kevinlutzer/room-environment-monitor/documentation/v2/3d.png

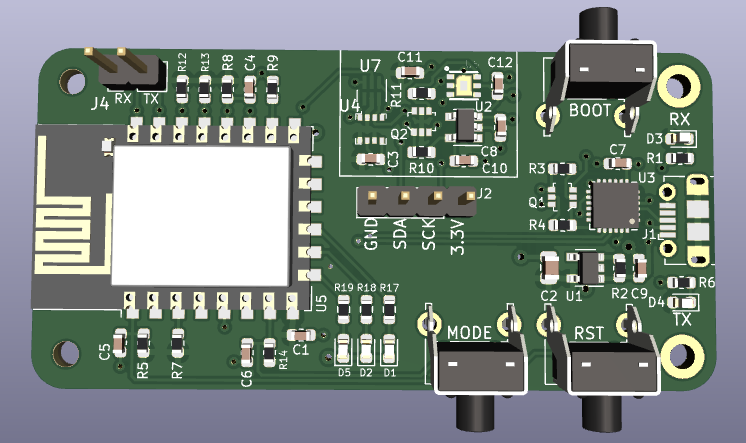
documentation/v2/3d.png
