kevinlutzer/room-environment-monitor/fab/v4/room-environment-monitor-v4/room_environment_monitor-F_Paste.pdf

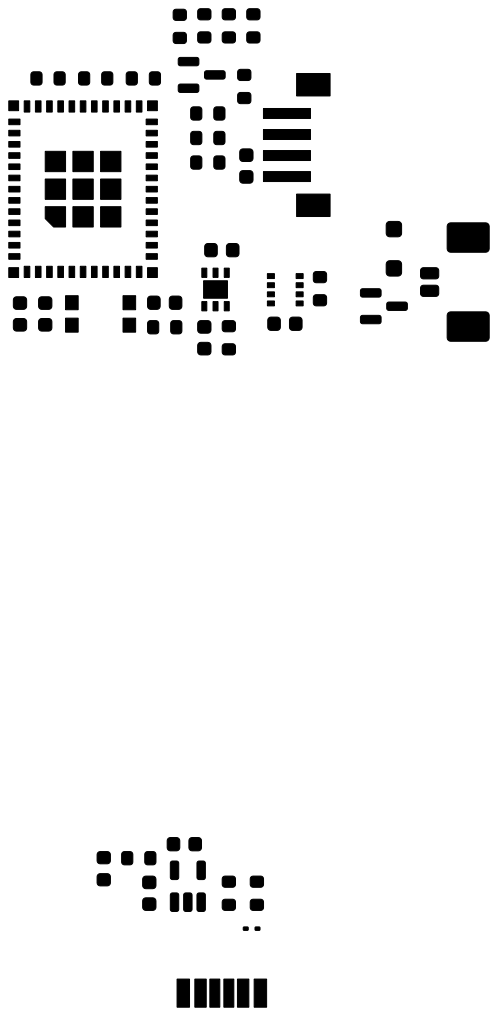
[picture p23: page 1]
