kevinlutzer/room-environment-monitor/fab/v4/room-environment-monitor-v4/room_environment_monitor-F_Silkscreen.pdf

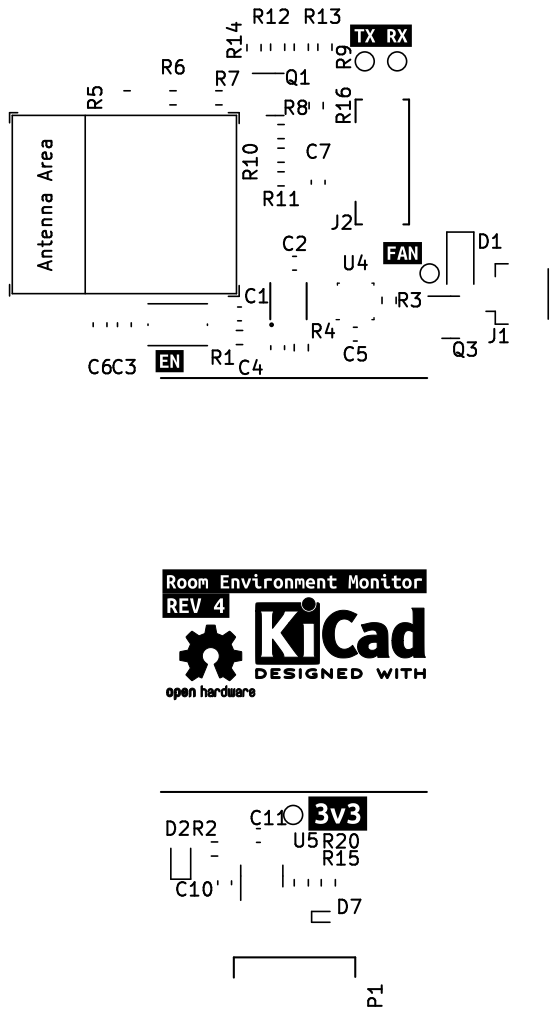
[picture p24: page 1]
