kevinlutzer/room-environment-monitor/fab/v4/room-environment-monitor-v4/room_environment_monitor-In1_Cu.pdf

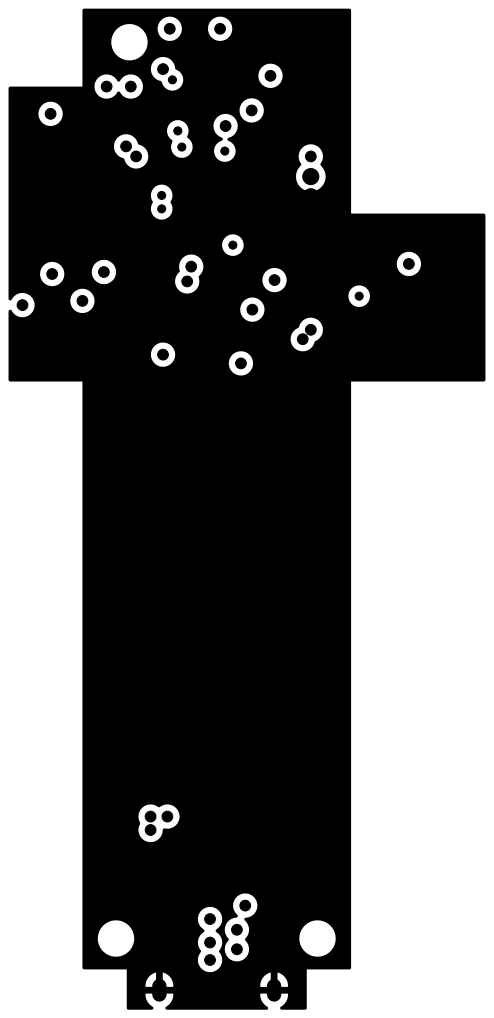
[picture p25: page 1]
