kevinlutzer/room-environment-monitor/fab/v4/room-environment-monitor-v4/room_environment_monitor-In2_Cu.pdf

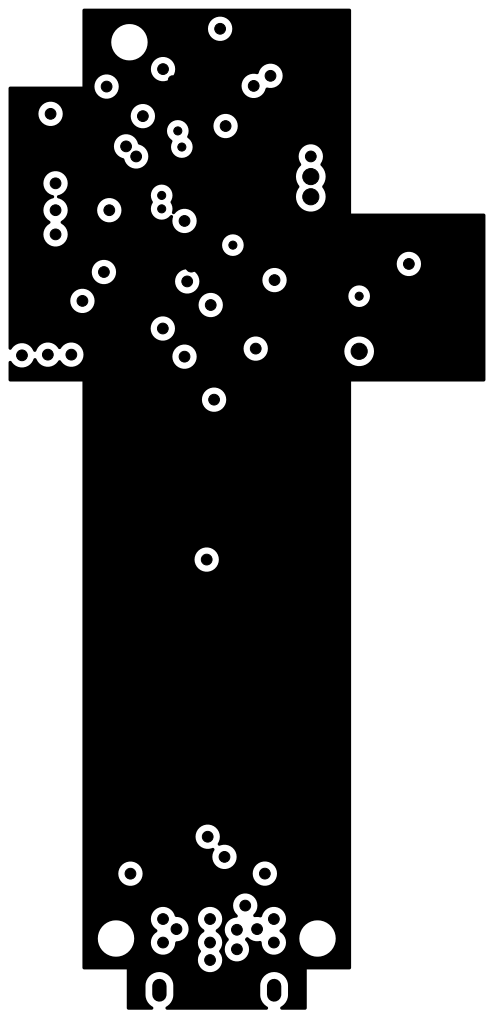
[picture p26: page 1]
